leaflabs/maplenative/STM32.sch

## KiCad design STM32.sch (2012-03-20, an earlier design)

Schematic: STM32.sch

Parts:
BUT1, BUT2: BUT
C1, C2: 18pF
C24, C25: 2.2uF
D4: LED
JP1: JP_SW
OSC1: 8Mhz
R1: 1.5k
R2: 10k
R18: 1k
U1: STM32F407ZE

Notes on the sheet:
solder jumper
