leaflabs/maplenative/bat.sch

## KiCad design bat.sch (2010-03-05)

Schematic: bat.sch

Parts:
BQ1: BQ24010DRC
C3, C7: 0.1uF
C4, C5, C6: 47uF
D1: DIODE
D2: Red
D3: Green
MCP1, MCP2: MCP1700T
P1, P3: CONN_2
P2: CONN_4X2
P4: CONN_6
R3, R4, R5: 1k
R6, R7: 10k
