leaflabs/maplenative/conn.sch

## KiCad design conn.sch (2012-03-20, an earlier design)

Schematic: conn.sch

Parts:
P5: CONN_5X2
P6: CONN_16X2
P7: CONN_16
P8, P9: CONN_32
SD1: SD
