leaflabs/maplenative/pwr.sch

## KiCad design pwr.sch (2012-03-20, an earlier design)

Schematic: pwr.sch

Parts:
C5, C6, C7, C8, C9, C10, C13, C14, C15, C16, C18, C19, C20: 0.1uF
C11, C12: 47pF
C17: 10uF
C21: 2.2uF
C22: 330pF
C23: 10pF
C26: 1.0uF
C27, C30, C31: 22uF
C28: 4.7uF
C29: 33pF
D1, D2: DIODE
D3: Green
L1: 3.3uH; Digikey P/N 587-2892-1-ND
L2: 2.2uH; Digikey P/N 587-2890-1-ND
MCP1700T1: MCP1700T
P1, P2: CONN_2
P4: CONN_6
Q1, Q2: NPN
R4, R17: 1K
R5: 3.01K
R6: 1k
R7: 47k
R8: 10k
R9, R10: 22
R11: 36k
R12, R19, R20: 1.5k
R13, R14, R15, R16: 10K
R21: 15K
R22: 324K
R23: 121K
R24: 105K
U3: LTC3566
USB1: USB
