leaflabs/maplenative/sram.sch

## KiCad design sram.sch (2012-03-20, an earlier design)

Schematic: sram.sch

Parts:
C3, C4: 0.1uF
R3: 10k
U2: IS62WV51216ALL
